lee26hwang12an/Adjustable_DC_Power_Supply_Unit/_firmware/App/app.h

#ifndef _APP_H_
#define _APP_H_

#ifdef __cplusplus
extern "C" {
#endif /* __cplusplus */


#include "main.h"

void setup();
void loop();


#ifdef __cplusplus
}
#endif /* __cplusplus */

#endif /* _APP_H_ */
